ooguzhanesen/PowerLoggerMini/output/stackup.jpeg

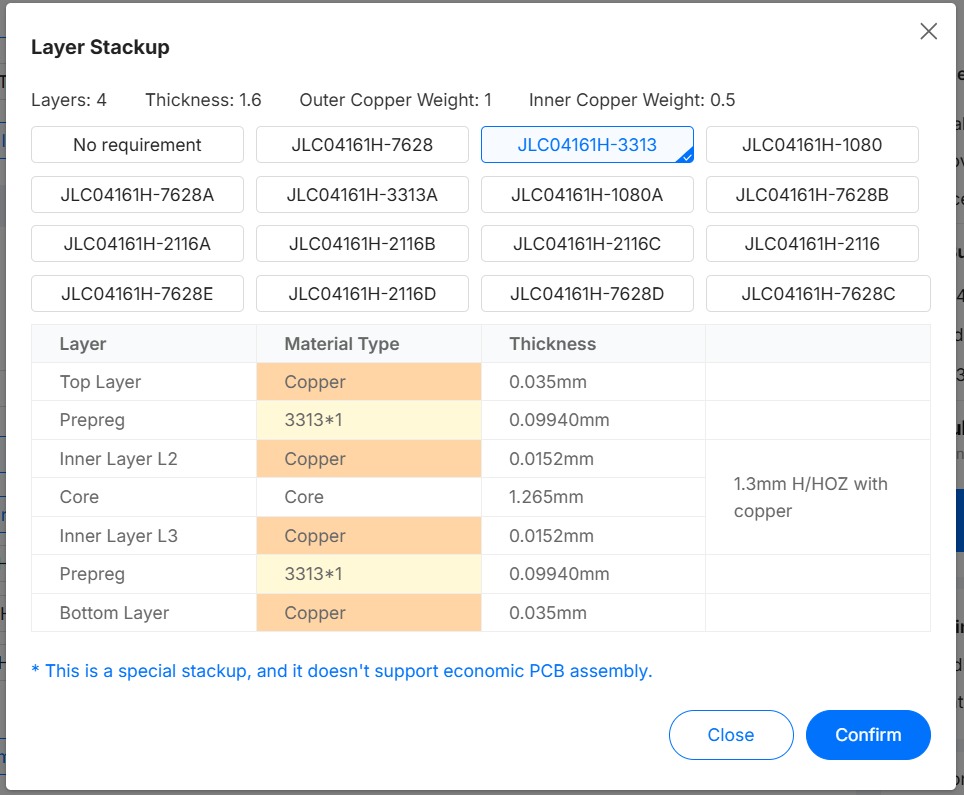
output/stackup.jpeg
